bwmott/U1MB600XL/images/IMG_3134.JPEG

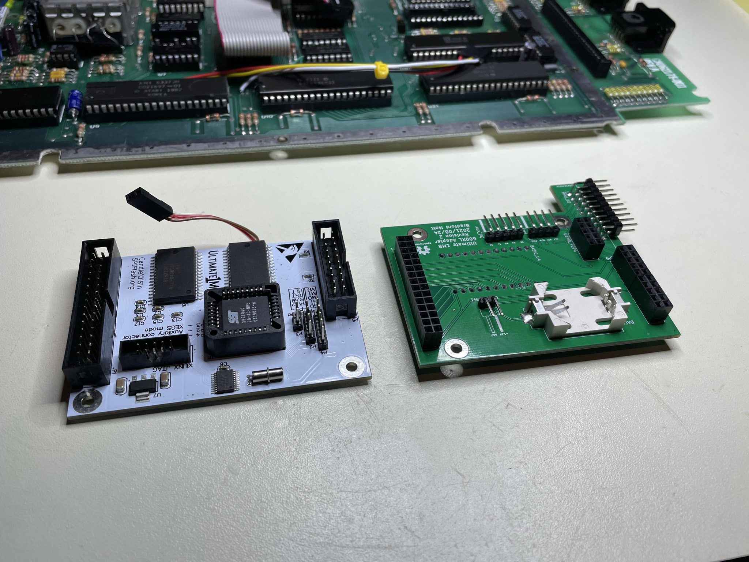
images/IMG_3134.JPEG
